coolerzanu/Lilac-V1/Other/Images - General/Front_Flower.png

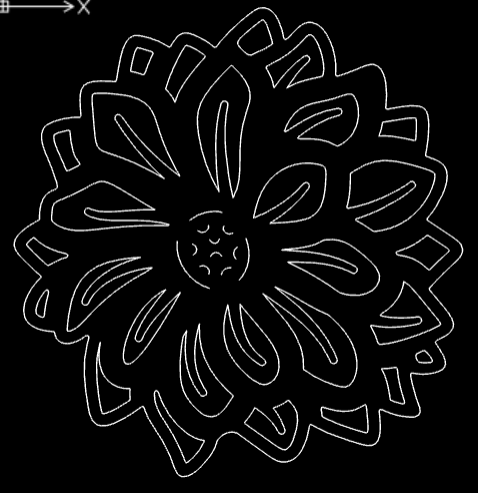
Other/Images - General/Front_Flower.png
