coolerzanu/Lilac-V1/Other/Images - General/Lilac-V1_(A5).png

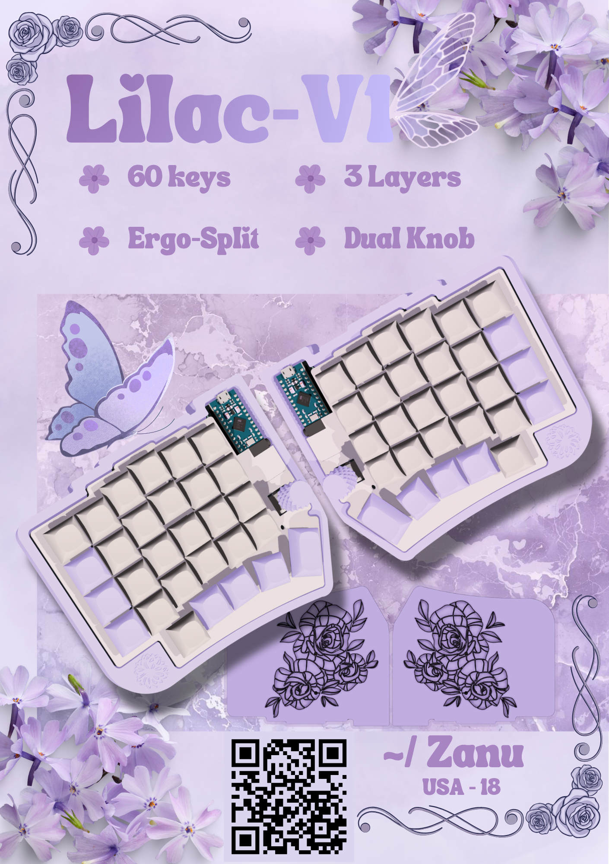
Other/Images - General/Lilac-V1_(A5).png
