coolerzanu/Lilac-V1/Other/Images - General/Schema_LED_Left.png

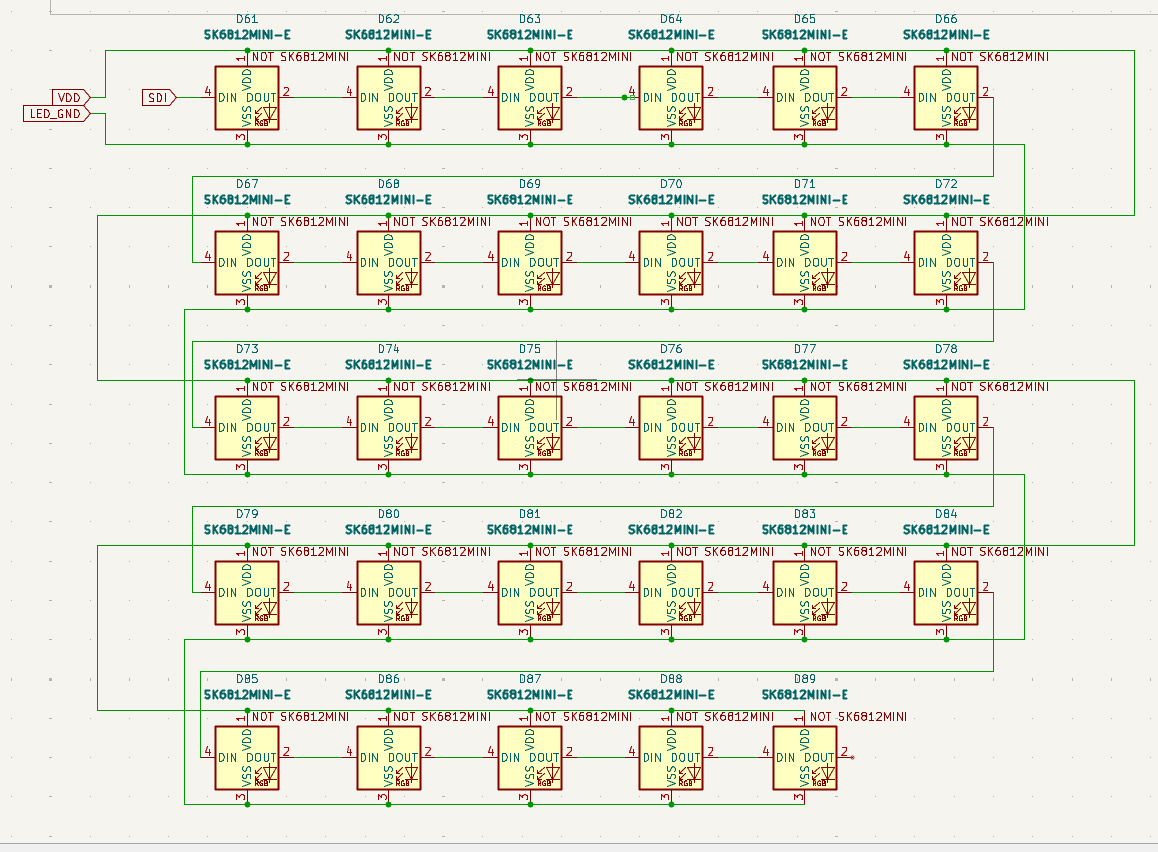
Other/Images - General/Schema_LED_Left.png
