coolerzanu/Lilac-V1/Other/Images - General/Schema_TRRS_Left.png

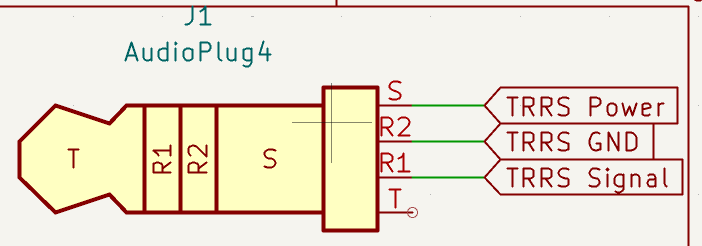
Other/Images - General/Schema_TRRS_Left.png
