coolerzanu/Lilac-V1/Other/Images - General/Screenshot 2026-04-06 181410.png

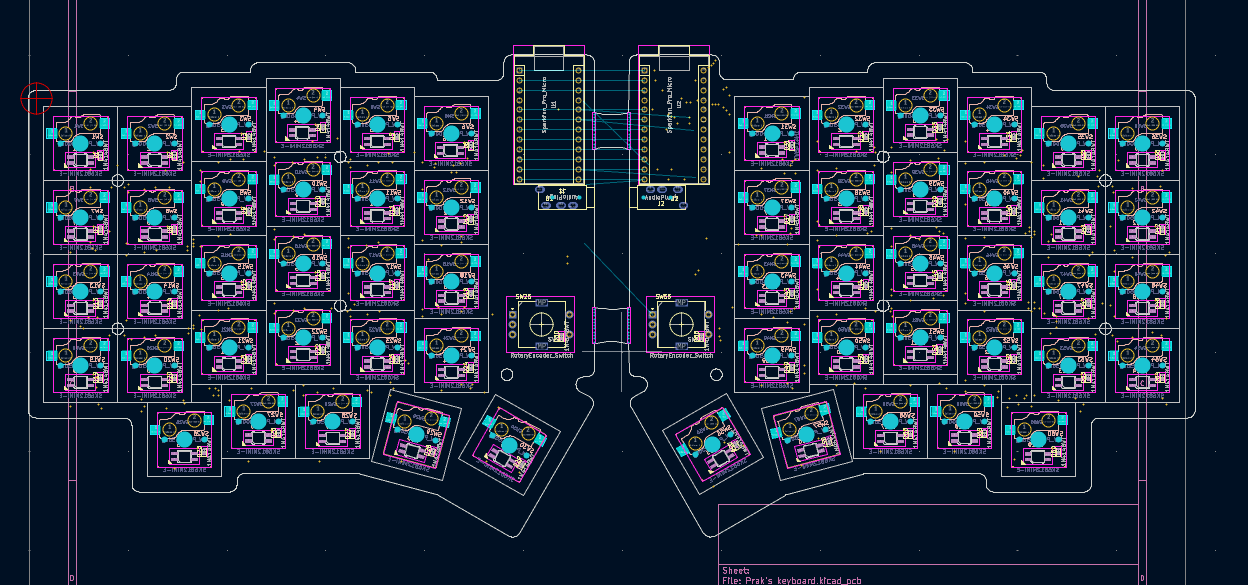
Other/Images - General/Screenshot 2026-04-06 181410.png
