coolerzanu/Lilac-V1/Hardware/PCB/side1.kicad_sch

## KiCad design Hardware/PCB/side1.kicad_sch (2026-04-26)

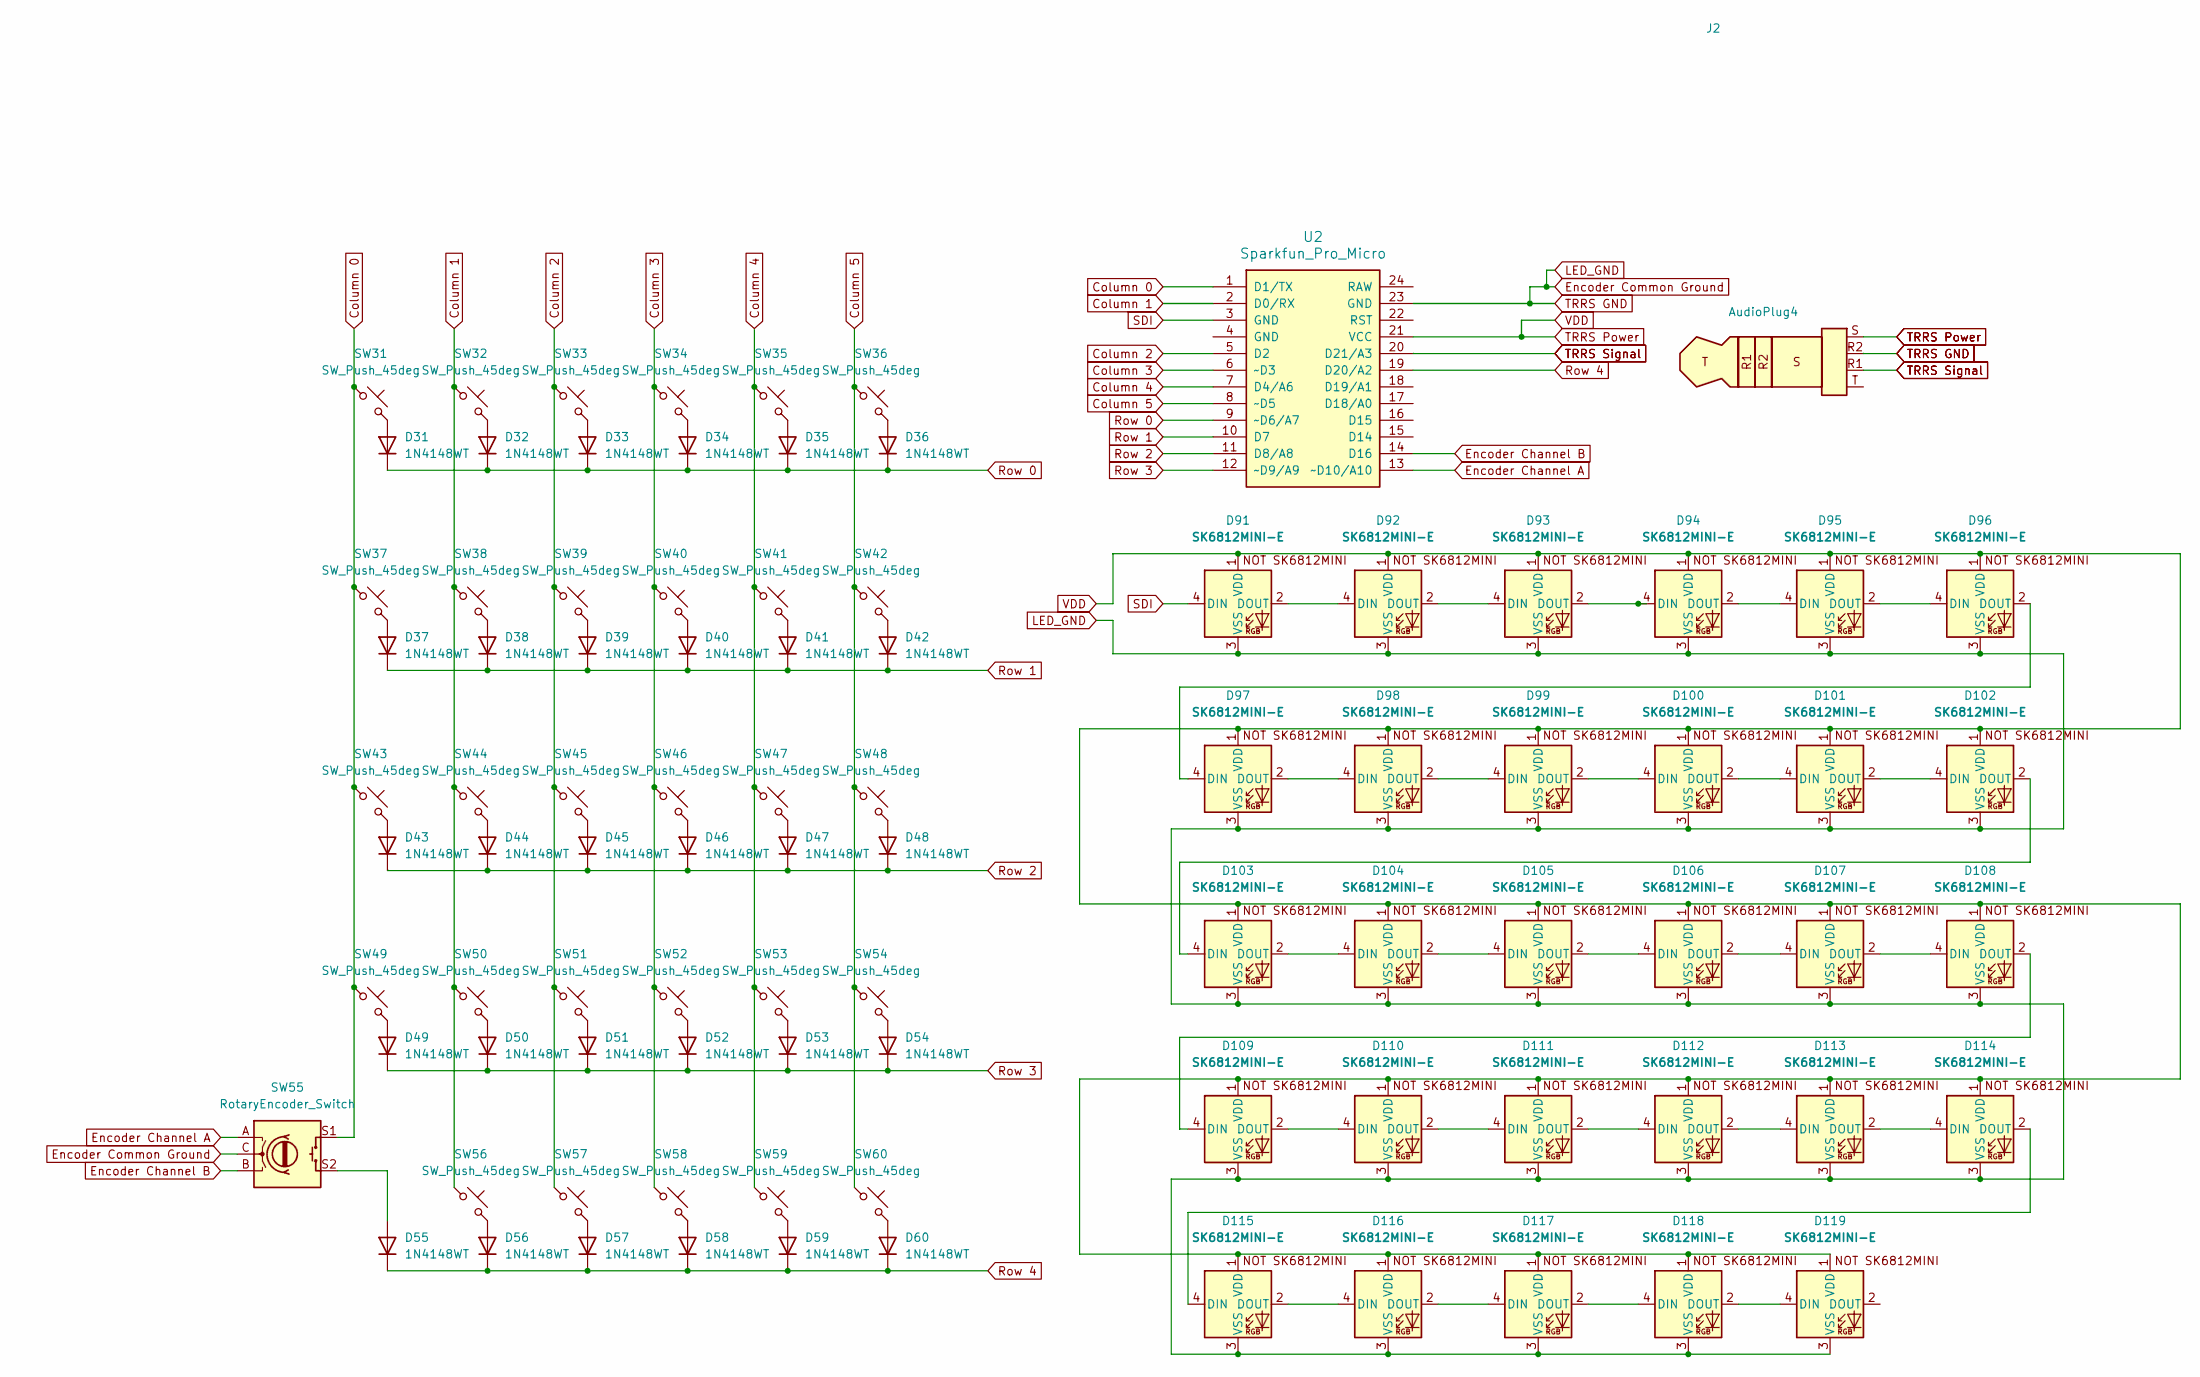
[picture p35: schematic side1.kicad_sch]

Parts:
D31, D32, D33, D34, D35, D36, D37, D38, D39, D40, D41, D42, D43, D44, D45, D46, D47, D48, D49, D50, D51, D52, D53, D54, D55, D56, D57, D58, D59, D60: 1N4148WT; D_SOD-523
D91, D92, D93, D94, D95, D96, D97, D98, D99, D100, D101, D102, D103, D104, D105, D106, D107, D108, D109, D110, D111, D112, D113, D114, D115, D116, D117, D118, D119: SK6812MINI-E; SK6812MINI-E_fixed
J2: AudioPlug4; CON_MJ-4PP-9
SW31, SW32, SW33, SW34, SW35, SW36, SW37, SW38, SW39, SW40, SW41, SW42, SW43, SW44, SW45, SW46, SW47, SW48, SW49, SW50, SW51, SW52, SW53, SW54, SW56, SW57, SW58, SW59, SW60: SW_Push_45deg; SW_MX_HS_KS-2P02B01-01_1u
SW55: RotaryEncoder_Switch; RotaryEncoder_Alps_EC11E-Switch_Vertical_H20mm
U2: Sparkfun_Pro_Micro

Connections:
Column 0: SW31.1, SW37.1, SW43.1, SW49.1, SW55.S1, U2.1 (D1/TX)
Column 1: SW32.1, SW38.1, SW44.1, SW50.1, SW56.1, U2.2 (D0/RX)
Column 2: SW33.1, SW39.1, SW45.1, SW51.1, SW57.1, U2.5 (D2)
Column 3: SW34.1, SW40.1, SW46.1, SW52.1, SW58.1, U2.6 (~D3)
Column 4: SW35.1, SW41.1, SW47.1, SW53.1, SW59.1, U2.7 (D4/A6)
Column 5: SW36.1, SW42.1, SW48.1, SW54.1, SW60.1, U2.8 (~D5)
Encoder Channel A: SW55.A, U2.13 (~D10/A10)
Encoder Channel B: SW55.B, U2.14 (D16)
Encoder Common Ground: D91.3 (VSS), D92.3 (VSS), D93.3 (VSS), D94.3 (VSS), D95.3 (VSS), D96.3 (VSS), D97.3 (VSS), D98.3 (VSS), D99.3 (VSS), D100.3 (VSS), D101.3 (VSS), D102.3 (VSS), D103.3 (VSS), D104.3 (VSS), D105.3 (VSS), D106.3 (VSS), D107.3 (VSS), D108.3 (VSS), D109.3 (VSS), D110.3 (VSS), D111.3 (VSS), D112.3 (VSS), D113.3 (VSS), D114.3 (VSS), D115.3 (VSS), D116.3 (VSS), D117.3 (VSS), D118.3 (VSS), D119.3 (VSS), J2.R2, SW55.C, U2.23 (GND)
unnamed: D31.2 (A), SW31.2
unnamed: D32.2 (A), SW32.2
unnamed: D33.2 (A), SW33.2
unnamed: D34.2 (A), SW34.2
unnamed: D35.2 (A), SW35.2
unnamed: D36.2 (A), SW36.2
unnamed: D37.2 (A), SW37.2
unnamed: D38.2 (A), SW38.2
unnamed: D39.2 (A), SW39.2
unnamed: D40.2 (A), SW40.2
unnamed: D41.2 (A), SW41.2
unnamed: D42.2 (A), SW42.2
unnamed: D43.2 (A), SW43.2
unnamed: D44.2 (A), SW44.2
unnamed: D45.2 (A), SW45.2
unnamed: D46.2 (A), SW46.2
unnamed: D47.2 (A), SW47.2
unnamed: D48.2 (A), SW48.2
unnamed: D49.2 (A), SW49.2
unnamed: D50.2 (A), SW50.2
unnamed: D51.2 (A), SW51.2
unnamed: D52.2 (A), SW52.2
unnamed: D53.2 (A), SW53.2
unnamed: D54.2 (A), SW54.2
unnamed: D55.2 (A), SW55.S2
unnamed: D56.2 (A), SW56.2
unnamed: D57.2 (A), SW57.2
unnamed: D58.2 (A), SW58.2
unnamed: D59.2 (A), SW59.2
unnamed: D60.2 (A), SW60.2
unnamed: D91.2 (DOUT), D92.4 (DIN)
unnamed: D92.2 (DOUT), D93.4 (DIN)
unnamed: D93.2 (DOUT), D94.4 (DIN)
unnamed: D94.2 (DOUT), D95.4 (DIN)
unnamed: D95.2 (DOUT), D96.4 (DIN)
unnamed: D96.2 (DOUT), D97.4 (DIN)
unnamed: D97.2 (DOUT), D98.4 (DIN)
unnamed: D98.2 (DOUT), D99.4 (DIN)
unnamed: D100.2 (DOUT), D101.4 (DIN)
unnamed: D99.2 (DOUT), D100.4 (DIN)
unnamed: D101.2 (DOUT), D102.4 (DIN)
unnamed: D102.2 (DOUT), D103.4 (DIN)
unnamed: D103.2 (DOUT), D104.4 (DIN)
unnamed: D104.2 (DOUT), D105.4 (DIN)
unnamed: D105.2 (DOUT), D106.4 (DIN)
unnamed: D106.2 (DOUT), D107.4 (DIN)
unnamed: D107.2 (DOUT), D108.4 (DIN)
unnamed: D108.2 (DOUT), D109.4 (DIN)
unnamed: D109.2 (DOUT), D110.4 (DIN)
unnamed: D110.2 (DOUT), D111.4 (DIN)
unnamed: D111.2 (DOUT), D112.4 (DIN)
unnamed: D112.2 (DOUT), D113.4 (DIN)
unnamed: D113.2 (DOUT), D114.4 (DIN)
unnamed: D114.2 (DOUT), D115.4 (DIN)
unnamed: D115.2 (DOUT), D116.4 (DIN)
unnamed: D116.2 (DOUT), D117.4 (DIN)
unnamed: D117.2 (DOUT), D118.4 (DIN)
unnamed: D118.2 (DOUT), D119.4 (DIN)
Row 0: D31.1 (K), D32.1 (K), D33.1 (K), D34.1 (K), D35.1 (K), D36.1 (K), U2.9 (~D6/A7)
Row 1: D37.1 (K), D38.1 (K), D39.1 (K), D40.1 (K), D41.1 (K), D42.1 (K), U2.10 (D7)
Row 2: D43.1 (K), D44.1 (K), D45.1 (K), D46.1 (K), D47.1 (K), D48.1 (K), U2.11 (D8/A8)
Row 3: D49.1 (K), D50.1 (K), D51.1 (K), D52.1 (K), D53.1 (K), D54.1 (K), U2.12 (~D9/A9)
Row 4: D55.1 (K), D56.1 (K), D57.1 (K), D58.1 (K), D59.1 (K), D60.1 (K), U2.19 (D20/A2)
SDI: D91.4 (DIN), U2.3 (GND)
TRRS Power: D91.1 (VDD), D92.1 (VDD), D93.1 (VDD), D94.1 (VDD), D95.1 (VDD), D96.1 (VDD), D97.1 (VDD), D98.1 (VDD), D99.1 (VDD), D100.1 (VDD), D101.1 (VDD), D102.1 (VDD), D103.1 (VDD), D104.1 (VDD), D105.1 (VDD), D106.1 (VDD), D107.1 (VDD), D108.1 (VDD), D109.1 (VDD), D110.1 (VDD), D111.1 (VDD), D112.1 (VDD), D113.1 (VDD), D114.1 (VDD), D115.1 (VDD), D116.1 (VDD), D117.1 (VDD), D118.1 (VDD), D119.1 (VDD), J2.S, U2.21 (VCC)
TRRS Signal: J2.R1, U2.20 (D21/A3)
