coolerzanu/Lilac-V1/Hardware/PCB/side.kicad_sch

## KiCad design Hardware/PCB/side.kicad_sch (2026-04-26)

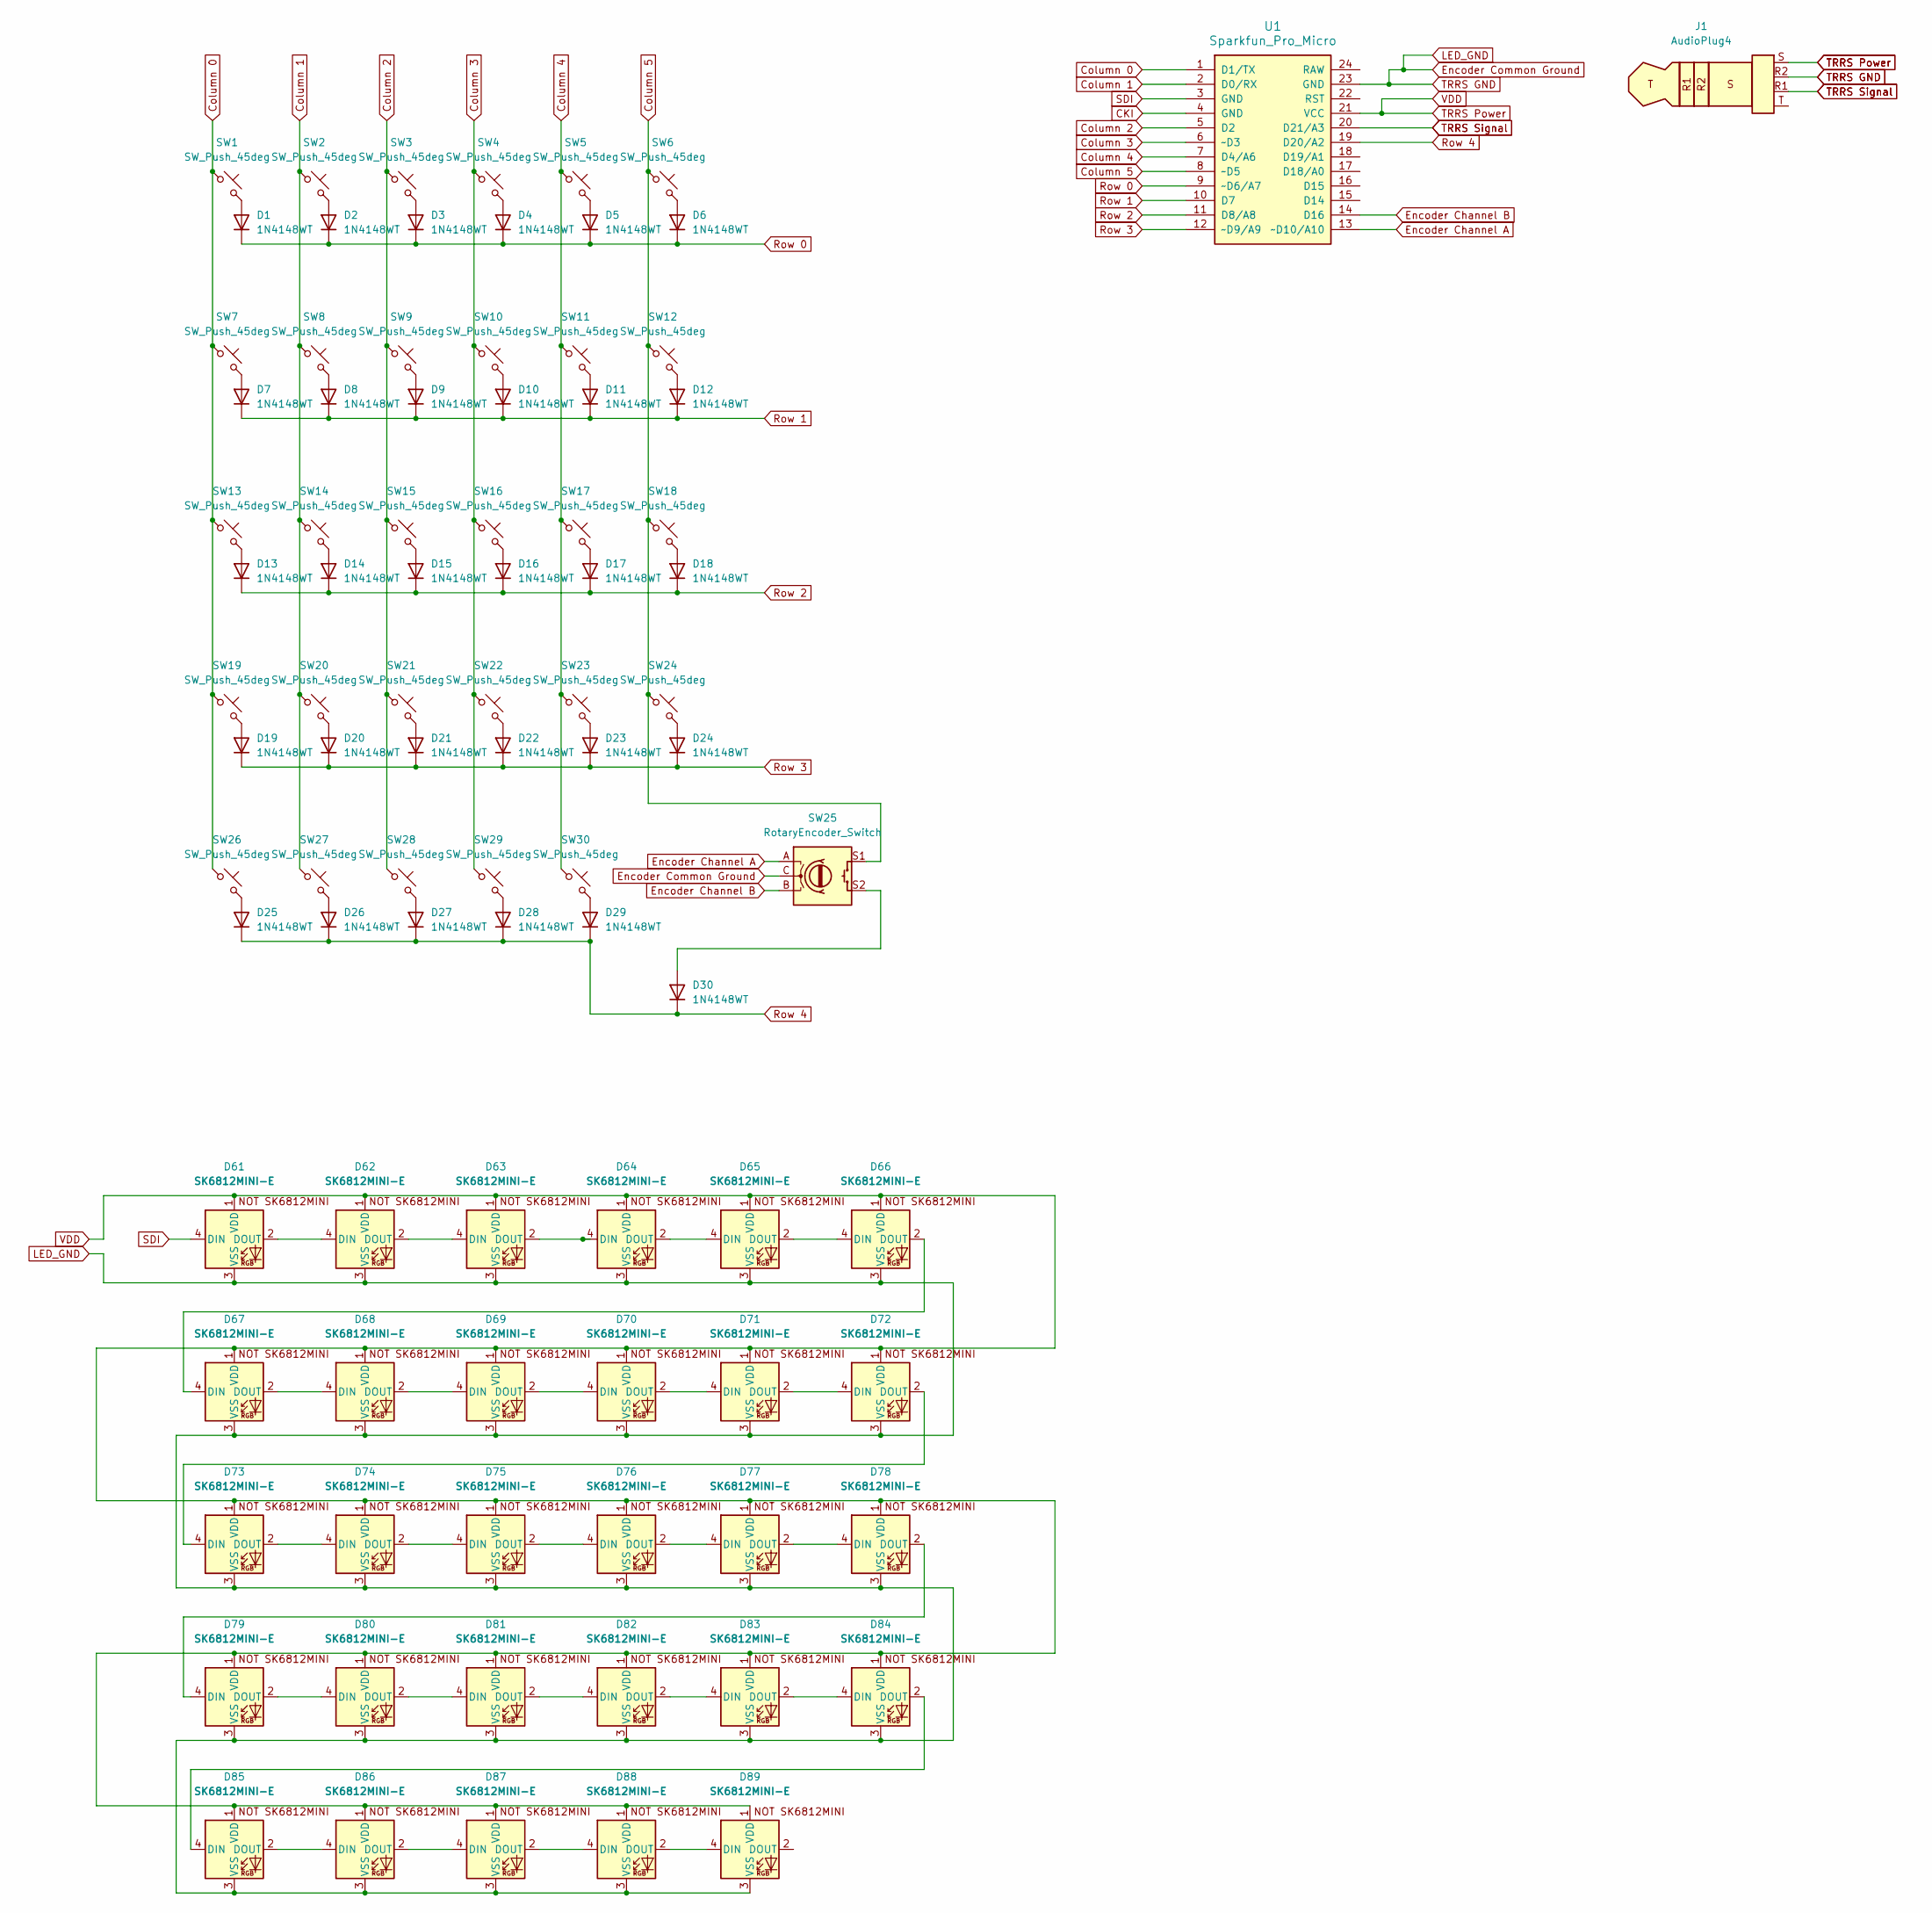
[picture p36: schematic side.kicad_sch]

Parts:
D1, D2, D3, D4, D5, D6, D7, D8, D9, D10, D11, D12, D13, D14, D15, D16, D17, D18, D19, D20, D21, D22, D23, D24, D25, D26, D27, D28, D29, D30: 1N4148WT; D_SOD-523
D61, D62, D63, D64, D65, D66, D67, D68, D69, D70, D71, D72, D73, D74, D75, D76, D77, D78, D79, D80, D81, D82, D83, D84, D85, D86, D87, D88, D89: SK6812MINI-E; SK6812MINI-E_fixed
J1: AudioPlug4; CON_MJ-4PP-9
SW1, SW2, SW3, SW4, SW5, SW6, SW7, SW8, SW9, SW10, SW11, SW12, SW13, SW14, SW15, SW16, SW17, SW18, SW19, SW20, SW21, SW22, SW23, SW24, SW26, SW27, SW28, SW29, SW30: SW_Push_45deg; SW_MX_HS_KS-2P02B01-01_1u
SW25: RotaryEncoder_Switch; RotaryEncoder_Alps_EC11E-Switch_Vertical_H20mm
U1: Sparkfun_Pro_Micro

Connections:
CKI: U1.4 (GND)
Column 0: SW1.1, SW7.1, SW13.1, SW19.1, SW26.1, U1.1 (D1/TX)
Column 1: SW2.1, SW8.1, SW14.1, SW20.1, SW27.1, U1.2 (D0/RX)
Column 2: SW3.1, SW9.1, SW15.1, SW21.1, SW28.1, U1.5 (D2)
Column 3: SW4.1, SW10.1, SW16.1, SW22.1, SW29.1, U1.6 (~D3)
Column 4: SW5.1, SW11.1, SW17.1, SW23.1, SW30.1, U1.7 (D4/A6)
Column 5: SW6.1, SW12.1, SW18.1, SW24.1, SW25.S1, U1.8 (~D5)
Encoder Channel A: SW25.A, U1.13 (~D10/A10)
Encoder Channel B: SW25.B, U1.14 (D16)
Encoder Common Ground: D61.3 (VSS), D62.3 (VSS), D63.3 (VSS), D64.3 (VSS), D65.3 (VSS), D66.3 (VSS), D67.3 (VSS), D68.3 (VSS), D69.3 (VSS), D70.3 (VSS), D71.3 (VSS), D72.3 (VSS), D73.3 (VSS), D74.3 (VSS), D75.3 (VSS), D76.3 (VSS), D77.3 (VSS), D78.3 (VSS), D79.3 (VSS), D80.3 (VSS), D81.3 (VSS), D82.3 (VSS), D83.3 (VSS), D84.3 (VSS), D85.3 (VSS), D86.3 (VSS), D87.3 (VSS), D88.3 (VSS), D89.3 (VSS), J1.R2, SW25.C, U1.23 (GND)
unnamed: D1.2 (A), SW1.2
unnamed: D2.2 (A), SW2.2
unnamed: D3.2 (A), SW3.2
unnamed: D4.2 (A), SW4.2
unnamed: D5.2 (A), SW5.2
unnamed: D6.2 (A), SW6.2
unnamed: D7.2 (A), SW7.2
unnamed: D8.2 (A), SW8.2
unnamed: D9.2 (A), SW9.2
unnamed: D10.2 (A), SW10.2
unnamed: D11.2 (A), SW11.2
unnamed: D12.2 (A), SW12.2
unnamed: D13.2 (A), SW13.2
unnamed: D14.2 (A), SW14.2
unnamed: D15.2 (A), SW15.2
unnamed: D16.2 (A), SW16.2
unnamed: D17.2 (A), SW17.2
unnamed: D18.2 (A), SW18.2
unnamed: D19.2 (A), SW19.2
unnamed: D20.2 (A), SW20.2
unnamed: D21.2 (A), SW21.2
unnamed: D22.2 (A), SW22.2
unnamed: D23.2 (A), SW23.2
unnamed: D24.2 (A), SW24.2
unnamed: D25.2 (A), SW26.2
unnamed: D26.2 (A), SW27.2
unnamed: D27.2 (A), SW28.2
unnamed: D28.2 (A), SW29.2
unnamed: D29.2 (A), SW30.2
unnamed: D30.2 (A), SW25.S2
unnamed: D61.2 (DOUT), D62.4 (DIN)
unnamed: D62.2 (DOUT), D63.4 (DIN)
unnamed: D63.2 (DOUT), D64.4 (DIN)
unnamed: D64.2 (DOUT), D65.4 (DIN)
unnamed: D65.2 (DOUT), D66.4 (DIN)
unnamed: D66.2 (DOUT), D67.4 (DIN)
unnamed: D67.2 (DOUT), D68.4 (DIN)
unnamed: D68.2 (DOUT), D69.4 (DIN)
unnamed: D69.2 (DOUT), D70.4 (DIN)
unnamed: D70.2 (DOUT), D71.4 (DIN)
unnamed: D71.2 (DOUT), D72.4 (DIN)
unnamed: D72.2 (DOUT), D73.4 (DIN)
unnamed: D73.2 (DOUT), D74.4 (DIN)
unnamed: D74.2 (DOUT), D75.4 (DIN)
unnamed: D75.2 (DOUT), D76.4 (DIN)
unnamed: D76.2 (DOUT), D77.4 (DIN)
unnamed: D77.2 (DOUT), D78.4 (DIN)
unnamed: D78.2 (DOUT), D79.4 (DIN)
unnamed: D79.2 (DOUT), D80.4 (DIN)
unnamed: D80.2 (DOUT), D81.4 (DIN)
unnamed: D81.2 (DOUT), D82.4 (DIN)
unnamed: D82.2 (DOUT), D83.4 (DIN)
unnamed: D83.2 (DOUT), D84.4 (DIN)
unnamed: D84.2 (DOUT), D85.4 (DIN)
unnamed: D85.2 (DOUT), D86.4 (DIN)
unnamed: D86.2 (DOUT), D87.4 (DIN)
unnamed: D87.2 (DOUT), D88.4 (DIN)
unnamed: D88.2 (DOUT), D89.4 (DIN)
Row 0: D1.1 (K), D2.1 (K), D3.1 (K), D4.1 (K), D5.1 (K), D6.1 (K), U1.9 (~D6/A7)
Row 1: D7.1 (K), D8.1 (K), D9.1 (K), D10.1 (K), D11.1 (K), D12.1 (K), U1.10 (D7)
Row 2: D13.1 (K), D14.1 (K), D15.1 (K), D16.1 (K), D17.1 (K), D18.1 (K), U1.11 (D8/A8)
Row 3: D19.1 (K), D20.1 (K), D21.1 (K), D22.1 (K), D23.1 (K), D24.1 (K), U1.12 (~D9/A9)
Row 4: D25.1 (K), D26.1 (K), D27.1 (K), D28.1 (K), D29.1 (K), D30.1 (K), U1.19 (D20/A2)
SDI: D61.4 (DIN), U1.3 (GND)
TRRS Power: D61.1 (VDD), D62.1 (VDD), D63.1 (VDD), D64.1 (VDD), D65.1 (VDD), D66.1 (VDD), D67.1 (VDD), D68.1 (VDD), D69.1 (VDD), D70.1 (VDD), D71.1 (VDD), D72.1 (VDD), D73.1 (VDD), D74.1 (VDD), D75.1 (VDD), D76.1 (VDD), D77.1 (VDD), D78.1 (VDD), D79.1 (VDD), D80.1 (VDD), D81.1 (VDD), D82.1 (VDD), D83.1 (VDD), D84.1 (VDD), D85.1 (VDD), D86.1 (VDD), D87.1 (VDD), D88.1 (VDD), D89.1 (VDD), J1.S, U1.21 (VCC)
TRRS Signal: J1.R1, U1.20 (D21/A3)
